moth754/Dart-Timer/Instructions/Images/Switch.jpg

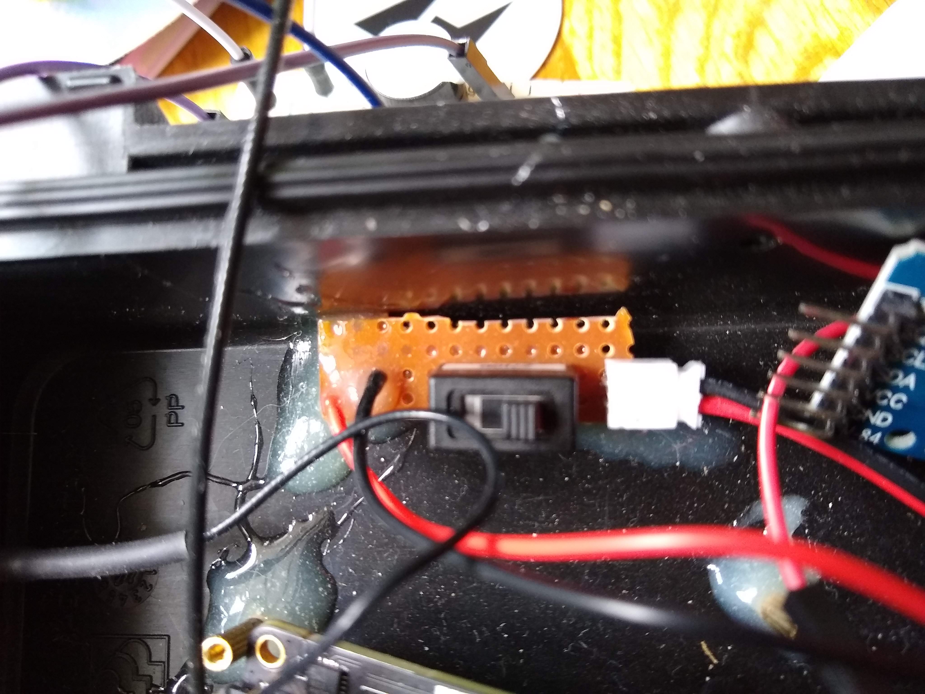
Instructions/Images/Switch.jpg
