moth754/Dart-Timer/Code for device/boot.py

# boot.py -- run on boot-up
#RGB LED setup
import pycom
#from network import WLAN
from machine import Pin

pycom.heartbeat(False) #turn off RGB LED - need that pin
#pycom.pybytes_on_boot(False) #turn off pybytes on boot

p=Pin('P12', mode=Pin.OUT)(True)
#wlan = WLAN()
#wlan.antenna(WLAN.EXT_ANTENNA)
